david-we/sisk/pics/left_sisk_3d.png

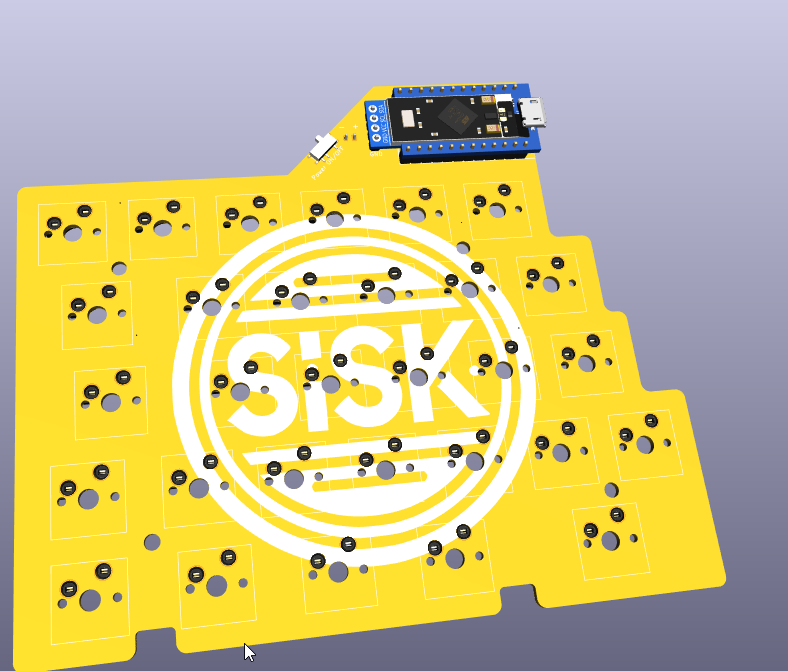
pics/left_sisk_3d.png
