david-we/sisk/pics/right_pcb_3d_front.PNG

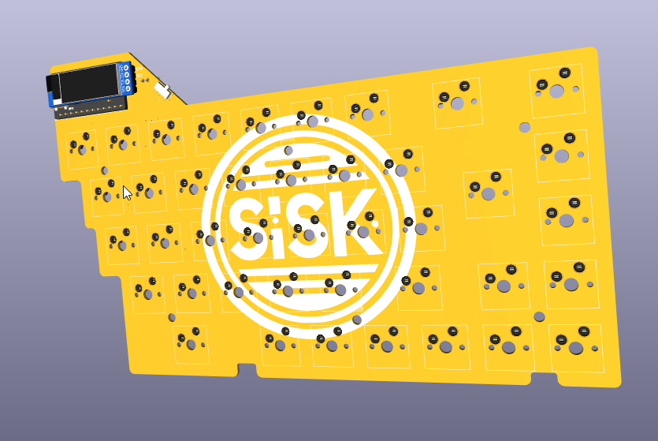
pics/right_pcb_3d_front.PNG
